CheNing233/XCN_CV-Programer_Keyboard/HAL/RTC.c

/********************************** (C) COPYRIGHT *******************************
 * File Name          : RTC.c
 * Author             : WCH
 * Version            : V1.2
 * Date               : 2022/01/18
 * Description        : RTC配置及其初始化
 *********************************************************************************
 * Copyright (c) 2021 Nanjing Qinheng Microelectronics Co., Ltd.
 * Attention: This software (modified or not) and binary are used for 
 * microcontroller manufactured by Nanjing Qinheng Microelectronics.
 *******************************************************************************/

/******************************************************************************/
/* 头文件包含 */
#include "HAL.h"

/*********************************************************************
 * CONSTANTS
 */
#define RTC_INIT_TIME_HOUR      0
#define RTC_INIT_TIME_MINUTE    0
#define RTC_INIT_TIME_SECEND    0

/***************************************************
 * Global variables
 */
volatile uint32_t RTCTigFlag;

/*******************************************************************************
 * @fn      RTC_SetTignTime
 *
 * @brief   配置RTC触发时间
 *
 * @param   time    - 触发时间.
 *
 * @return  None.
 */
void RTC_SetTignTime(uint32_t time) {
    sys_safe_access_enable();
    R32_RTC_TRIG = time;
    RTCTigFlag = 0;
    sys_safe_access_disable();
}

/*******************************************************************************
 * @fn      RTC_IRQHandler
 *
 * @brief   RTC中断处理
 *
 * @param   None.
 *
 * @return  None.
 */
__attribute__((interrupt("WCH-Interrupt-fast")))
__attribute__((section(".highcode")))
void RTC_IRQHandler(void) {
    R8_RTC_FLAG_CTRL = (RB_RTC_TMR_CLR | RB_RTC_TRIG_CLR);
    RTCTigFlag = 1;
}

/*******************************************************************************
 * @fn      HAL_Time0Init
 *
 * @brief   系统定时器初始化
 *
 * @param   None.
 *
 * @return  None.
 */
void HAL_TimeInit(void) {
#if(CLK_OSC32K)
    sys_safe_access_enable();
    R8_CK32K_CONFIG &= ~(RB_CLK_OSC32K_XT | RB_CLK_XT32K_PON);
    sys_safe_access_enable();
    R8_CK32K_CONFIG |= RB_CLK_INT32K_PON;
    Lib_Calibration_LSI();
#else
    sys_safe_access_enable();
    R8_CK32K_CONFIG |= RB_CLK_OSC32K_XT | RB_CLK_INT32K_PON | RB_CLK_XT32K_PON;
#endif
    sys_safe_access_disable();
    RTC_InitTime(2020, 1, 1, 0, 0, 0); //RTC时钟初始化当前时间
    TMOS_TimerInit(0);
}

/******************************** endfile @ time ******************************/
